nicolasagostino/TDIII/Documentos/Esquemático/DispositivoDeLocalizaciónYSeguimiento/DispositivoDeLocalizaciónYSeguimiento.kicad_sch

## KiCad design Documentos/Esquemático/DispositivoDeLocalizaciónYSeguimiento/DispositivoDeLocalizaciónYSeguimiento.kicad_sch (2023-11-30)

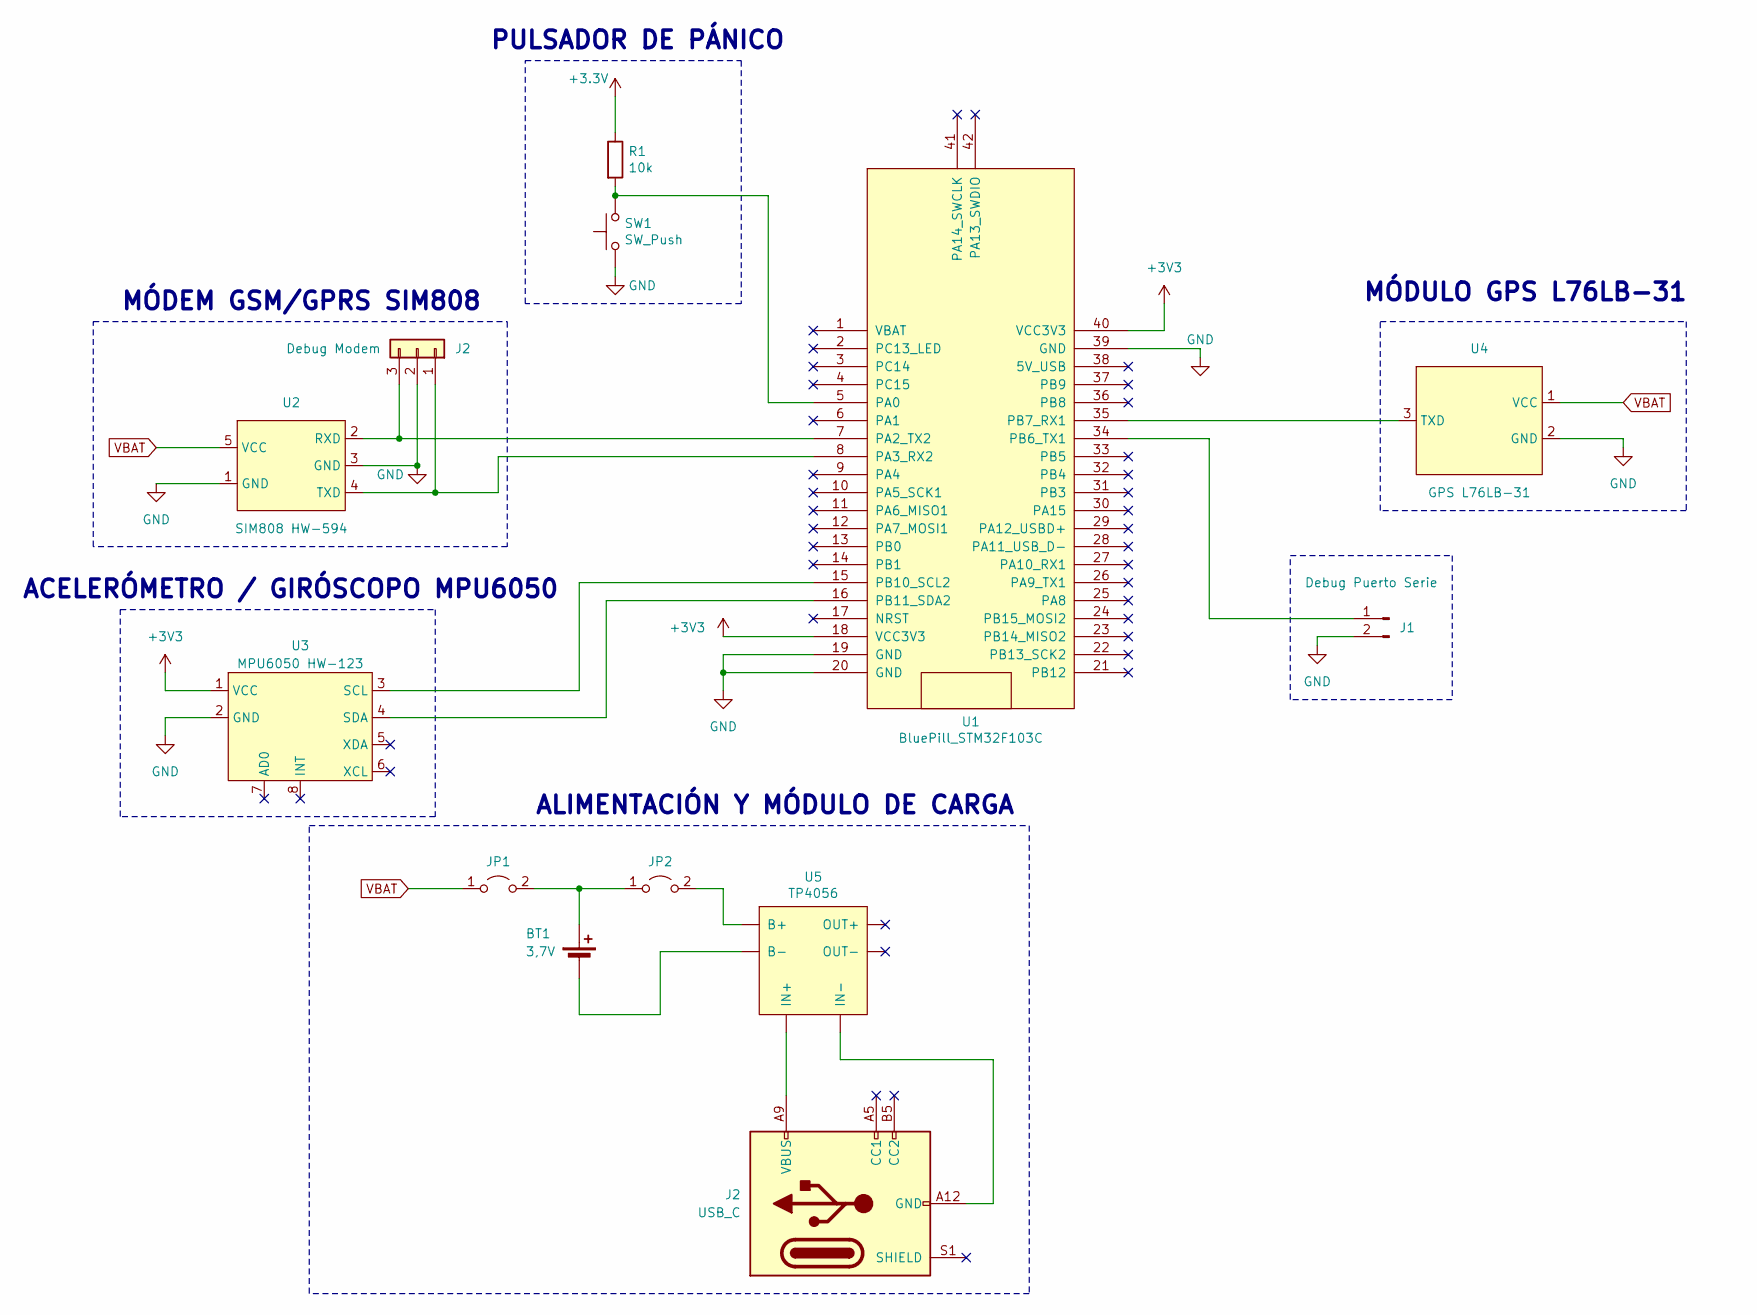
[picture p38: schematic DispositivoDeLocalizaciónYSeguimiento.kicad_sch]

Parts:
BT1: 3,7V
J1: Debug Puerto Serie
J2: Debug Modem
JP1, JP2: Jumper_2_Open
R1: 10k; R_Axial_DIN0207_L6.3mm_D2.5mm_P10.16mm_Horizontal
SW1: SW_Push; SW_PUSH_6mm_H13mm
U1: BluePill_STM32F103C
U2: SIM808 HW-594; SIM808_HW-594
U3: MPU6050 HW-123
U4: GPS L76LB-31; GPS_L76LB-31
U5: TP4056

Connections:
+3.3V: R1.1
+3V3: U1.18 (VCC3V3), U1.40 (VCC3V3), U3.1 (VCC)
GND: J1.2, J2.2, SW1.1, U1.19 (GND), U1.20 (GND), U1.39 (GND), U2.1 (GND), U2.3 (GND), U3.2 (GND), U4.2 (GND)
unnamed: BT1.1 (+), JP1.2 (B), JP2.1 (A)
unnamed: BT1.2 (-), U5.~
unnamed: J1.1, U1.34 (PB6_TX1)
unnamed: J2.1, U1.8 (PA3_RX2), U2.4 (TXD)
unnamed: J2.3, U1.7 (PA2_TX2), U2.2 (RXD)
unnamed: J2.A9 (VBUS), J2.B9 (VBUS), U5.~
unnamed: J2.A12 (GND), J2.B12 (GND), U5.~
unnamed: JP2.2 (B), U5.~
unnamed: R1.2, SW1.2, U1.5 (PA0)
unnamed: U1.15 (PB10_SCL2), U3.3 (SCL)
unnamed: U1.16 (PB11_SDA2), U3.4 (SDA)
unnamed: U1.35 (PB7_RX1), U4.3 (TXD)
VBAT: JP1.1 (A), U2.5 (VCC), U4.1 (VCC)

Notes on the sheet:
MÓDEM GSM/GPRS SIM808
PULSADOR DE PÁNICO
ALIMENTACIÓN Y MÓDULO DE CARGA
ACELERÓMETRO / GIRÓSCOPO MPU6050
MÓDULO GPS L76LB-31
