nicolasagostino/TDIII/Proyecto_Localizador/Core/Inc/Globals.h

/*
 * Globals.h
 *
 *  Created on: Jun 14, 2022
 *      Author: edgardog
 */

#ifndef INC_GLOBALS_H_
#define INC_GLOBALS_H_

#include "stm32f1xx_hal.h"
#include "fatfs.h"

#ifdef USE_RTC_SPI
extern RTC_HandleTypeDef *pRTC;

typedef enum
{
  HAL_RTC_STATE_RESET             = 0x00U,  /*!< RTC not yet initialized or disabled */
  HAL_RTC_STATE_READY             = 0x01U,  /*!< RTC initialized and ready for use   */
  HAL_RTC_STATE_BUSY              = 0x02U,  /*!< RTC process is ongoing              */
  HAL_RTC_STATE_TIMEOUT           = 0x03U,  /*!< RTC timeout state                   */
  HAL_RTC_STATE_ERROR             = 0x04U   /*!< RTC error state                     */

} HAL_RTCStateTypeDef;

typedef struct
{
  uint32_t AsynchPrediv;    /*!< Specifies the RTC Asynchronous Predivider value.
                                 This parameter must be a number between Min_Data = 0x00 and Max_Data = 0xFFFFF  or RTC_AUTO_1_SECOND
                                 If RTC_AUTO_1_SECOND is selected, AsynchPrediv will be set automatically to get 1sec timebase */

  uint32_t OutPut;          /*!< Specifies which signal will be routed to the RTC Tamper pin.
                                 This parameter can be a value of @ref RTC_output_source_to_output_on_the_Tamper_pin */

} RTC_InitTypeDef;

typedef struct
{
  uint8_t WeekDay;  /*!< Specifies the RTC Date WeekDay (not necessary for HAL_RTC_SetDate).
                         This parameter can be a value of @ref RTC_WeekDay_Definitions */

  uint8_t Month;    /*!< Specifies the RTC Date Month (in BCD format).
                         This parameter can be a value of @ref RTC_Month_Date_Definitions */

  uint8_t Date;     /*!< Specifies the RTC Date.
                         This parameter must be a number between Min_Data = 1 and Max_Data = 31 */

  uint8_t Year;     /*!< Specifies the RTC Date Year.
                         This parameter must be a number between Min_Data = 0 and Max_Data = 99 */

} RTC_DateTypeDef;

typedef struct
{
  RTC_TypeDef                 *Instance;  /*!< Register base address    */

  RTC_InitTypeDef             Init;       /*!< RTC required parameters  */

  RTC_DateTypeDef             DateToUpdate;       /*!< Current date set by user and updated automatically  */

  HAL_LockTypeDef             Lock;       /*!< RTC locking object       */

  __IO HAL_RTCStateTypeDef    State;      /*!< Time communication state */
} RTC_HandleTypeDef;
#endif

//Archivos SD
extern uint8_t retUSER;
extern char USERPath[4];
extern FATFS USERFatFS;
extern FIL USERFile;

#endif /* INC_GLOBALS_H_ */
